ECE411-Fall2021-Group4/RF-Tin-Can/LTSpice/Band_Pass_Filters.asc

C1: cap; {C}
C2: cap; {C2}
C3: cap; {C}
C4: cap; {C3}
C5: cap; {C4}
C6: cap; {C3}
L1: ind; {L}
L2: ind; {L2}
L3: ind; {L}
L4: ind; {L3}
L5: ind; {L4}
L6: ind; {L3}
R1: res; 50
R2: res; 50
V1: voltage; ""; AC 1; Rser=50
V2: voltage; ""; AC 1; Rser=50
Named nets: 0
.param C 5.6n
.param L 220n
.param C2 56p
.param L2 22u
.ac lin 10000 10 1G
4.5MHz
.param C3 12n
.param C4 120p
.ac lin 10000 10 1G
.param L3 47n
.param L4 4.7u
6.5MHz
