ECE411-Fall2021-Group4/RF-Tin-Can/LTSpice/Low_Pass_Filters.asc

C1: cap; {C2}
C2: cap; {C4}
C3: cap; {C4}
C4: cap; {C2}
C5: cap; {C}
C6: cap; {C}
C7: cap; {C3}
C8: cap; {C3}
L1: ind; {L}
L2: ind; {L}
L3: ind; {L}
L4: ind; {L2}
L5: ind; {L2}
L6: ind; {L2}
R1: res; 50
R2: res; 50
V1: voltage; ""; AC 1; Rser=50
V2: voltage; ""; AC 1; Rser=50
Named nets: 0
.ac lin 1000 1 1G
.param C 470p
.param L 1.2u
.param C2 1n
6.5MHz
.ac lin 1000 1 1G
.param C3 470p
.param L2 3.3u
.param C4 1n
4.5MHz
